MarekZegare4/ESP32_tracker/src/tracking/imu_calibration/imu_calibration.h

class correctionData {
    public:
        double A[3][3] = {0};
        double b[3] = {0};
};

class CalibratedIMUData {
    public:
        float x;
        float y;
        float z;
};

void readCalibrationData(float x, float y, float z, int i);
void calibrate();
void sendCalculated();
void hardIronCorrection(float x, float y, float z);
CalibratedIMUData calibratedMagData(float x, float y, float z);
