MarekZegare4/ESP32_tracker/src/gui/gui.h

#pragma once
#include <Arduino.h>
#include "common/mavlink.h"
#include <Adafruit_GFX.h>
#include <Adafruit_SharpMem.h>
#include <mat.h>
#include <SPI.h>
#include "gfx.h"

enum eButton
{
	BUTTON_1,
	BUTTON_2,
	BUTTON_3,
	BUTTON_4,
	NONE
};

enum eFunctionType {
	SINGLE,	// Run this function once, activating it again will not do anything
	LOOP,	// Run this function in a loop
	TOGGLE,
};

class DisplayElements {	
	public:
		String gcsCompass;
		String mavStatusMsg;
		float attitudeRoll = 0;
		bool isConnected = false;
};

class Menu {
	public:
		const char *name;
		class MenuElement *elements;
		int elementCount;
		int selectedElement;
		class Menu *parent;
};

class MenuElement {
	public:
		const char *name;
		void (*function)(void * parameters);
		void * parameters;
		enum eFunctionType functionType;
		bool functionToggle;
		class Menu *subMenu;
}; 

void mainScreen();
void artificialHorizon();
void guiTask(void * parameters);
void degTask(void * parameters);
void guiInitialize();
void sendAttitude(mavlink_attitude_t attitude);
