MarekZegare4/ESP32_tracker/src/gui/gfx.h

#include <Arduino.h>

const unsigned char epd_bitmap_Interface_Essential_Alert_Circle_1__Streamline_Pixel [] PROGMEM = {
		0xff, 0x0f, 0xf0, 0xfc, 0x03, 0xf0, 0xf0, 0x00, 0xf0, 0xe1, 0xf8, 0x70, 0xc1, 0xf8, 0x30, 0xc1, 
	0xe8, 0x30, 0x81, 0xe8, 0x10, 0x81, 0xf8, 0x10, 0x01, 0xf8, 0x00, 0x00, 0xf0, 0x00, 0x00, 0xf0, 
	0x00, 0x00, 0x00, 0x00, 0x80, 0x60, 0x10, 0x80, 0xf0, 0x10, 0xc0, 0xf0, 0x30, 0xc0, 0xf0, 0x30, 
	0xe0, 0xf0, 0x70, 0xf0, 0x00, 0xf0, 0xfc, 0x03, 0xf0, 0xff, 0x0f, 0xf0
};
const unsigned char crosshair [] PROGMEM = {
	0xff, 0xf0, 0x03, 0xff, 0xc0, 0x92, 0x50, 0x02, 0x49, 0x40, 0xc9, 0x30, 0x03, 0x24, 0xc0, 0xff, 
	0xbf, 0xfe, 0xff, 0xc0, 0x00, 0x84, 0x92, 0x40, 0x00, 0x00, 0xd2, 0x49, 0x40, 0x00, 0x00, 0xff, 
	0xff, 0xc0, 0x00
};
